AleDedor/Dummy-Audio-amplifier/LTSpice/amp_cell.asc

C1: cap; 1000µ
C2: cap; 100µ
C3: cap; 10µ
C4: cap; 100µ
C5: cap; 100µ
C6: cap; 10µ
C7: cap; 1µ
C8: cap; 2µ
D1: diode
D2: diode
D3: diode
D4: diode
D5: diode
D6: diode
D7: diode
D8: diode
I1: current; ""; AC 20m
IT: current; ""; AC 30m
L1: ind; 0.91m
L2: ind; 0.91m
Q1: npn; 2N2222
Q2: pnp; 2N2907
Q3: npn; 2N2222
Q4: pnp; 2N2907
Q5: npn; 2N2222
Q6: pnp; 2N2907
Q7: npn; 2N2222
Q8: pnp; 2N2907
Q9: npn; 2N2222
Q10: pnp; 2N2907
R1: res; 1k
R2: res; 1k
R3: res; 10k
R4: res; 470
R5: res; 1k
R6: res; 22
R7: res; 1k
R8: res; 1k
R9: res; 1k
R10: res; 10k
R11: res; 470
R12: res; 1k
R13: res; 1k
R14: res; 22
R15: res; 1k
R16: res; 1k
R17: res; 1k
R18: res; 22
R19: res; 22
R20: res; 22
R21: res; 22
R22: res; 1k
R23: res; 1k
R24: res; 22
R25: res; 22
R26: res; 10k
R27: res; 10k
SPEAKER1: res; 16.8
SPEAKER: res; 16.8
U1: UniversalOpAmp; Avol=200k GBW=1.5Meg Vos=0
U2: UniversalOpAmp; Avol=200k GBW=1.5Meg Vos=0
U3: UniversalOpamp2; Avol=200k GBW=1.5Meg Slew=10Meg; Ilimit=25m Rail=2 Vos=0
U4: UniversalOpAmp; Avol=200k GBW=1.5Meg Vos=0
U5: UniversalOpAmp; Avol=200k GBW=1.5Meg Vos=0
V1: voltage; 18
V2: voltage; SINE(0 200m 1k)
V3: voltage; ""; AC 30m
V4: voltage; ""; AC 30m
Named nets: Vcc, 0, right+, AMP, Vout, BUFF, left+, Vbetha, test, Valpha, Valpha2, Vbetha2, VT, V_impedance
.ac dec 100 0.01 1Meg
OUTPUT POWER BUFFER (-60dB THD) AT FULL SWING
0.5W+0.5WMAX
2V MAX
INPUT FROM JACK = 0.5V MAX
AMPLIFIER X12dB - VOLTAGE SHIFTER WITH ZERO
INPUT FROM JACK = 0.1V MAX
GAIN IS 1 AT DC, 4 AT HF
AT LEAST 9V SO BUFFER IS NOT CLIPPING
.noise V(vout) V3 dec 100 0.1 1meg
1. STARTED WITH 200nV/Hz1/2 and BW = (20kHz - 34 Hz)
2. DECREASED BIASING AND GAIN RESISTORS, GOT 60nV/hz1/2
.tran 0 10m 0
ZOBEL NETWORK
CLASS B,.GOOD BUT STILL A LOT OF CROSSOVER DISTORTION
CLASS AB, LIKE THIS IS AFFECTED BY THERMAL RUNAWAY
