AleDedor/Dummy-Audio-amplifier/Performance/stage1_stable.png

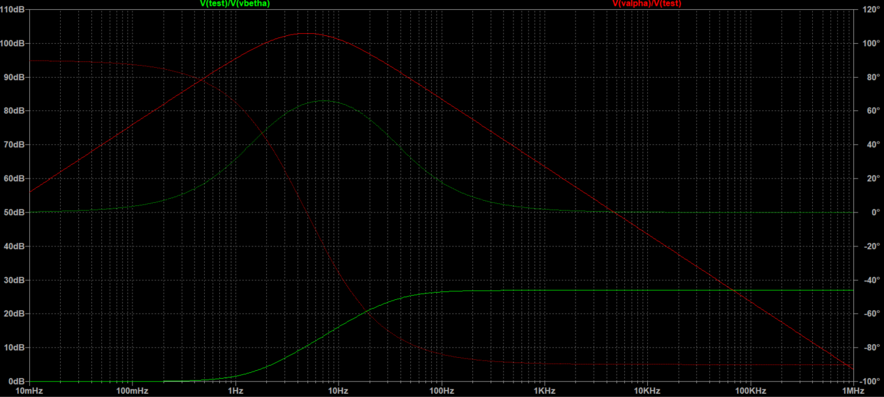
Performance/stage1_stable.png
